somepin/qalble/case/split/Wedge right.stl

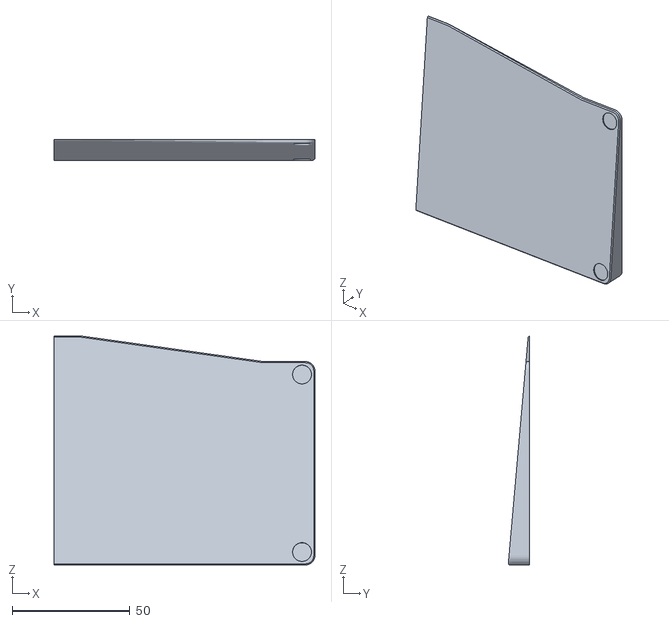
[picture p26: CAD file, 2022-01-31]
case/split/Wedge right.stl
110.6 x 9.07 x 97.0
