somepin/qalble/case/split/Bottom right.stl

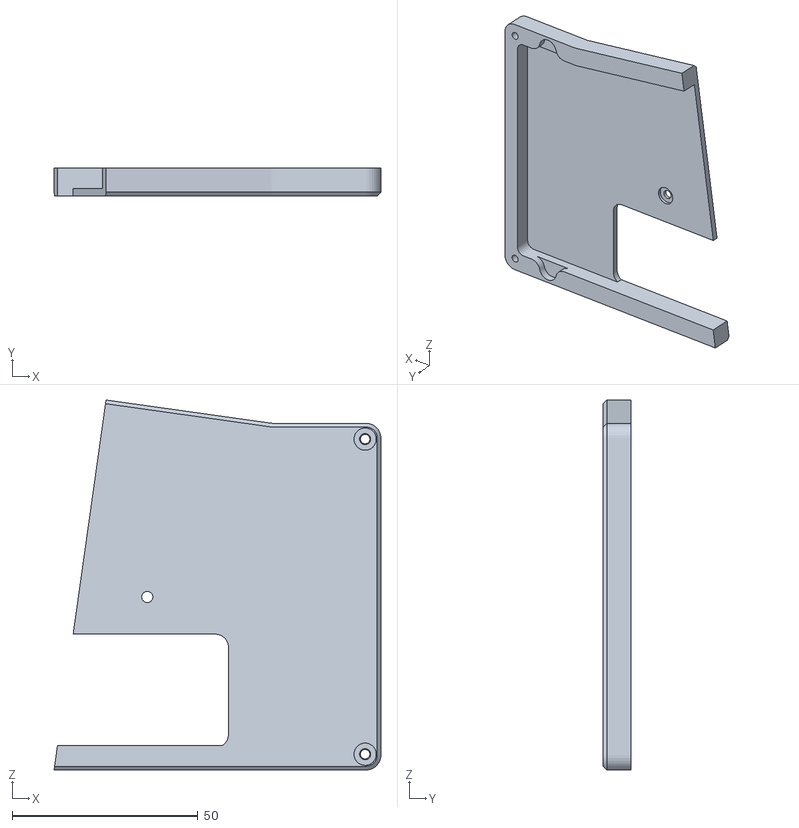
[picture p27: CAD file, 2022-01-31]
case/split/Bottom right.stl
87.9 x 7.50 x 99.5
