somepin/qalble/pcb/QALBLE.kicad_sch

## KiCad design pcb/QALBLE.kicad_sch (2022-01-31)

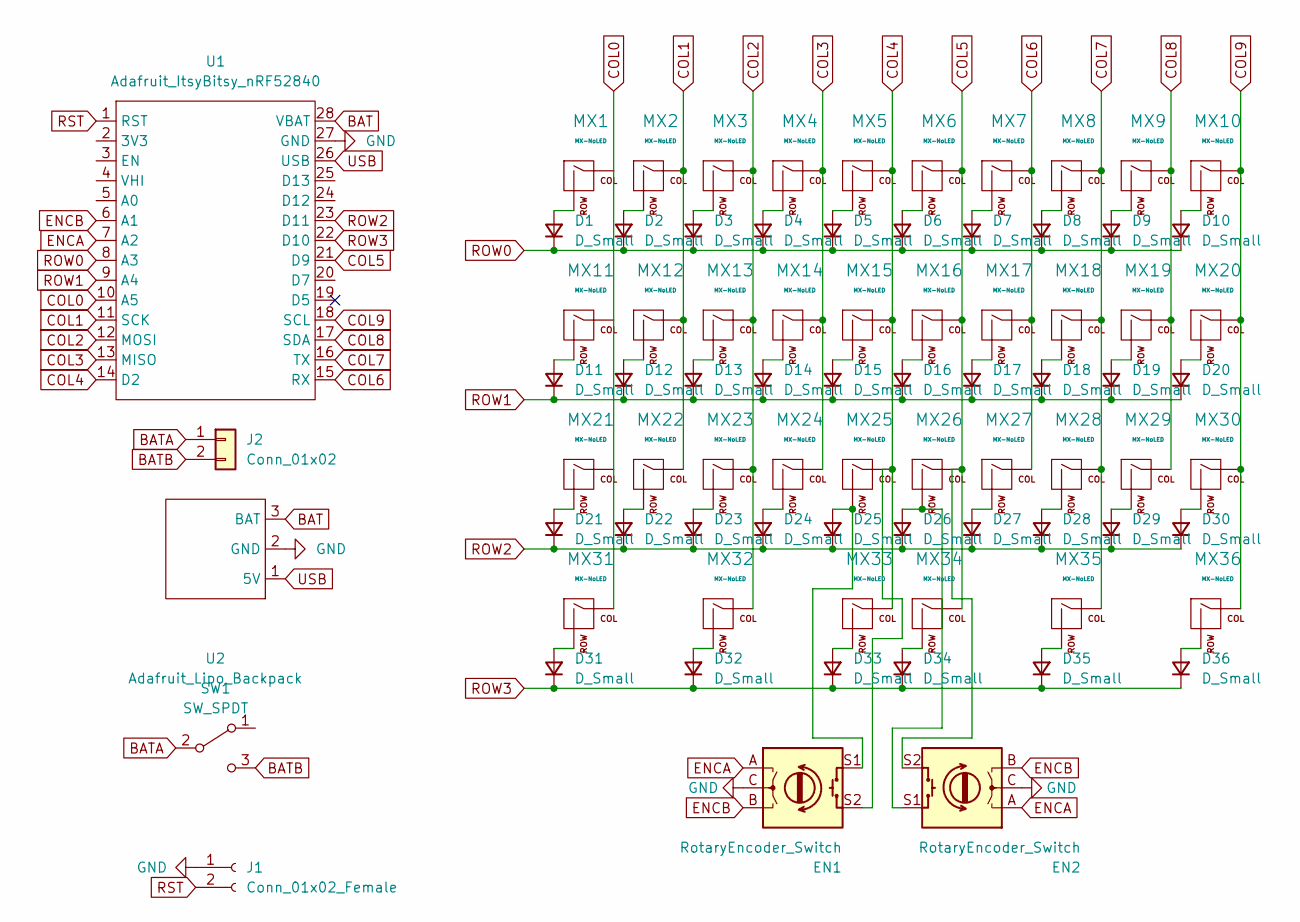
[picture p28: schematic QALBLE.kicad_sch]

Parts:
D1, D2, D3, D4, D5, D6, D7, D8, D9, D10, D11, D12, D13, D14, D15, D16, D17, D18, D19, D20, D21, D22, D23, D24, D25, D26, D27, D28, D29, D30, D31, D32, D33, D34, D35, D36: D_Small; Diode-Hybrid-Back
EN1, EN2: RotaryEncoder_Switch; RotaryEncoder_EC11
J1: Conn_01x02_Female; PinHeader_1x02_P2.54mm_Vertical
J2: Conn_01x02; Backpack Battery Jumper
MX1, MX2, MX3, MX4, MX5, MX6, MX7, MX8, MX9, MX12, MX13, MX14, MX15, MX16, MX17, MX18, MX19, MX20, MX22, MX23, MX24, MX25, MX26, MX27, MX28, MX29, MX31, MX32, MX35, MX36: MX-NoLED; MXOnly-1U-NoLED
MX10, MX11: MX-NoLED; MXOnly-1.25U-NoLED
MX21: MX-NoLED; MXOnly-1.75U-NoLED
MX30: MX-NoLED; MXOnly-1.5U-NoLED
MX33: MX-NoLED; MXOnly-2.25U-ReversedStabilizers-NoLED
MX34: MX-NoLED; MXOnly-2U-ReversedStabilizers-NoLED
SW1: SW_SPDT; SW_CuK_OS102011MA1QN1_SPDT_Angled
U1: Adafruit_ItsyBitsy_nRF52840; ItsyBitsy nRF52840
U2: Adafruit_Lipo_Backpack; Trinket Lipo Backpack

Connections:
BAT: U1.28 (VBAT), U2.3 (BAT)
BATA: J2.1, SW1.2 (B)
BATB: J2.2, SW1.3 (C)
COL0: MX1.1 (COL), MX11.1 (COL), MX21.1 (COL), MX31.1 (COL), U1.10 (A5)
COL1: MX2.1 (COL), MX12.1 (COL), MX22.1 (COL), U1.11 (SCK)
COL2: MX3.1 (COL), MX13.1 (COL), MX23.1 (COL), MX32.1 (COL), U1.12 (MOSI)
COL3: MX4.1 (COL), MX14.1 (COL), MX24.1 (COL), U1.13 (MISO)
COL4: EN1.S2, MX5.1 (COL), MX15.1 (COL), MX25.1 (COL), MX33.1 (COL), U1.14 (D2)
COL5: EN2.S2, MX6.1 (COL), MX16.1 (COL), MX26.1 (COL), MX34.1 (COL), U1.21 (D9)
COL6: MX7.1 (COL), MX17.1 (COL), MX27.1 (COL), U1.15 (RX)
COL7: MX8.1 (COL), MX18.1 (COL), MX28.1 (COL), MX35.1 (COL), U1.16 (TX)
COL8: MX9.1 (COL), MX19.1 (COL), MX29.1 (COL), U1.17 (SDA)
COL9: MX10.1 (COL), MX20.1 (COL), MX30.1 (COL), MX36.1 (COL), U1.18 (SCL)
ENCA: EN1.A, EN2.A, U1.7 (A2)
ENCB: EN1.B, EN2.B, U1.6 (A1)
GND: EN1.C, EN2.C, J1.1, U1.27 (GND), U2.2 (GND)
unnamed: D1.2 (A), MX1.2 (ROW)
unnamed: D2.2 (A), MX2.2 (ROW)
unnamed: D3.2 (A), MX3.2 (ROW)
unnamed: D4.2 (A), MX4.2 (ROW)
unnamed: D5.2 (A), MX5.2 (ROW)
unnamed: D6.2 (A), MX6.2 (ROW)
unnamed: D7.2 (A), MX7.2 (ROW)
unnamed: D8.2 (A), MX8.2 (ROW)
unnamed: D9.2 (A), MX9.2 (ROW)
unnamed: D10.2 (A), MX10.2 (ROW)
unnamed: D11.2 (A), MX11.2 (ROW)
unnamed: D12.2 (A), MX12.2 (ROW)
unnamed: D13.2 (A), MX13.2 (ROW)
unnamed: D14.2 (A), MX14.2 (ROW)
unnamed: D15.2 (A), MX15.2 (ROW)
unnamed: D16.2 (A), MX16.2 (ROW)
unnamed: D17.2 (A), MX17.2 (ROW)
unnamed: D18.2 (A), MX18.2 (ROW)
unnamed: D19.2 (A), MX19.2 (ROW)
unnamed: D20.2 (A), MX20.2 (ROW)
unnamed: D21.2 (A), MX21.2 (ROW)
unnamed: D22.2 (A), MX22.2 (ROW)
unnamed: D23.2 (A), MX23.2 (ROW)
unnamed: D24.2 (A), MX24.2 (ROW)
unnamed: D25.2 (A), EN1.S1, MX25.2 (ROW)
unnamed: D26.2 (A), EN2.S1, MX26.2 (ROW)
unnamed: D27.2 (A), MX27.2 (ROW)
unnamed: D28.2 (A), MX28.2 (ROW)
unnamed: D29.2 (A), MX29.2 (ROW)
unnamed: D30.2 (A), MX30.2 (ROW)
unnamed: D31.2 (A), MX31.2 (ROW)
unnamed: D32.2 (A), MX32.2 (ROW)
unnamed: D33.2 (A), MX33.2 (ROW)
unnamed: D34.2 (A), MX34.2 (ROW)
unnamed: D35.2 (A), MX35.2 (ROW)
unnamed: D36.2 (A), MX36.2 (ROW)
ROW0: D1.1 (K), D2.1 (K), D3.1 (K), D4.1 (K), D5.1 (K), D6.1 (K), D7.1 (K), D8.1 (K), D9.1 (K), D10.1 (K), U1.8 (A3)
ROW1: D11.1 (K), D12.1 (K), D13.1 (K), D14.1 (K), D15.1 (K), D16.1 (K), D17.1 (K), D18.1 (K), D19.1 (K), D20.1 (K), U1.9 (A4)
ROW2: D21.1 (K), D22.1 (K), D23.1 (K), D24.1 (K), D25.1 (K), D26.1 (K), D27.1 (K), D28.1 (K), D29.1 (K), D30.1 (K), U1.23 (D11)
ROW3: D31.1 (K), D32.1 (K), D33.1 (K), D34.1 (K), D35.1 (K), D36.1 (K), U1.22 (D10)
RST: J1.2, U1.1 (RST)
USB: U1.26 (USB), U2.1 (5V)
